rusefi/m74.9/hardware/m749.kicad_pcb

## KiCad design hardware/AWAC02.kicad_sch

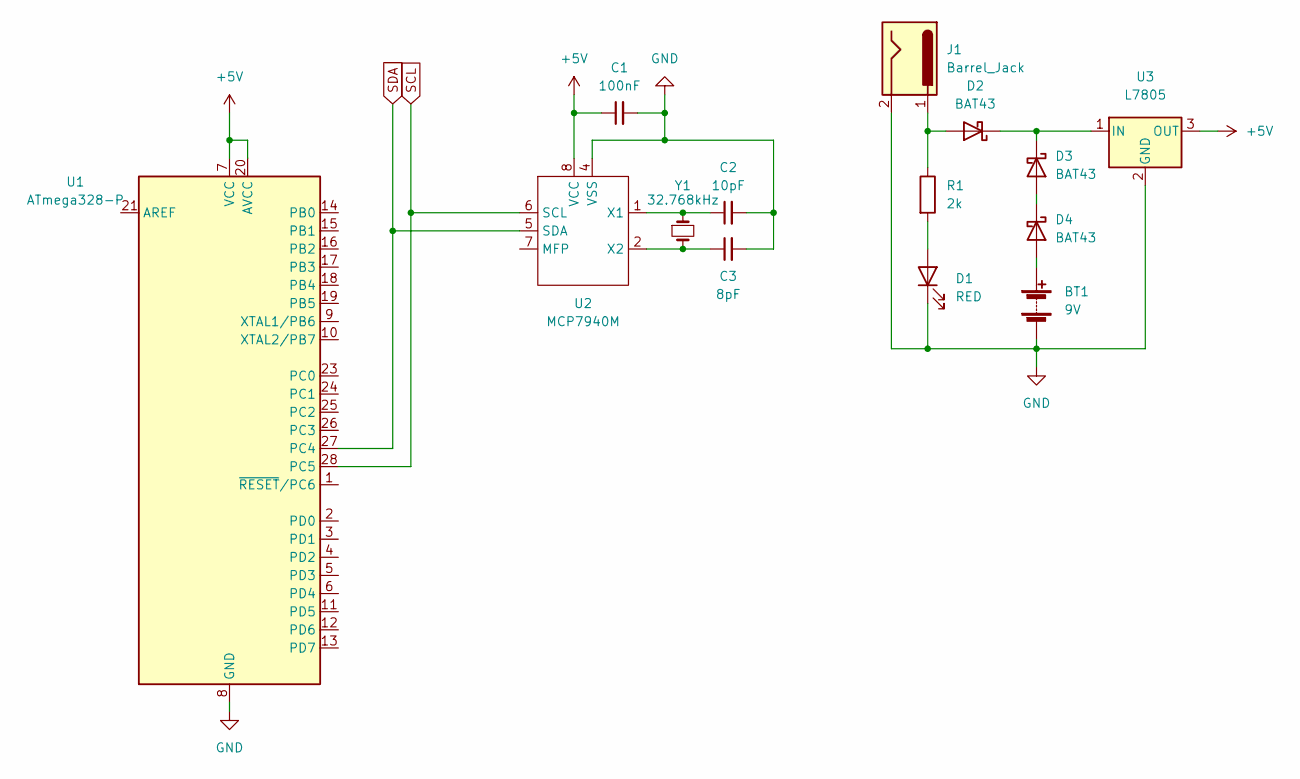
[picture p8: schematic AWAC02.kicad_sch]

Parts:
BT1: 9V
C1: 100nF
C2: 10pF
C3: 8pF
D1: RED
D2, D3, D4: BAT43; D_DO-35_SOD27_P7.62mm_Horizontal
J1: Barrel_Jack; BarrelJack_SwitchcraftConxall_RAPC10U_Horizontal
R1: 2k
U1: ATmega328-P; DIP-28_W7.62mm_Socket
U2: MCP7940M; DIP-8_W7.62mm_Socket
U3: L7805; TO-220-3_Vertical
Y1: 32.768kHz

Connections:
+5V: C1.1, U1.7 (VCC), U1.20 (AVCC), U2.8 (VCC), U3.3 (OUT)
GND: BT1.2 (-), C1.2, C2.2, C3.2, D1.1 (K), J1.2, U1.8 (GND), U1.22 (GND), U2.4 (VSS), U3.2 (GND)
unnamed: BT1.1 (+), D4.2 (A)
unnamed: C2.1, U2.1 (X1), Y1.1
unnamed: C3.1, U2.2 (X2), Y1.2
unnamed: D1.2 (A), R1.2
unnamed: D2.1 (K), D3.1 (K), U3.1 (IN)
unnamed: D2.2 (A), J1.1, R1.1
unnamed: D3.2 (A), D4.1 (K)
SCL: U1.28 (PC5), U2.6 (SCL)
SDA: U1.27 (PC4), U2.5 (SDA)
